kuvychko/session-beacon/host/tests/test_fixtures.py

"""Replay real Claude Code hook payloads through the state machine.

The payloads in tests/fixtures/hook_payloads.jsonl were captured from this
machine by running the daemon with --capture, not written by hand. That matters:
the published schema this project was originally built against disagrees with
what Claude Code 2.1.261 actually sends, and only a captured payload catches
that. See docs/claude-code-integration.md.

Conversation content is stripped at capture time, so the fixtures carry field
names and shapes and none of the text.
"""

from __future__ import annotations

import json
from pathlib import Path

import pytest

from beacon_host.capture import redact
from beacon_host.state import SessionStore, State

FIXTURES_DIR = Path(__file__).parent / "fixtures"
FIXTURES = FIXTURES_DIR / "hook_payloads.jsonl"
BACKGROUND_STOP = FIXTURES_DIR / "stop_with_background_tasks.json"
SUBAGENT_RUN = FIXTURES_DIR / "subagent_run.jsonl"


def load() -> dict[str, dict]:
    lines = FIXTURES.read_text(encoding="utf-8").splitlines()
    payloads = [json.loads(line) for line in lines if line.strip()]
    return {p["hook_event_name"]: p for p in payloads}


@pytest.fixture(scope="module")
def events() -> dict[str, dict]:
    return load()


def test_fixtures_cover_the_observed_lifecycle(events):
    assert set(events) == {
        "SessionStart", "UserPromptSubmit", "PermissionRequest", "PostToolUse",
        "PostToolBatch", "Notification", "Stop", "SessionEnd"
    }


def test_every_payload_has_the_fields_the_state_machine_reads(events):
    """session_id, cwd and hook_event_name are the three the store depends on."""
    for name, p in events.items():
        assert p.get("session_id"), name
        assert p.get("cwd"), name
        assert p.get("hook_event_name") == name


def test_real_lifecycle_drives_the_expected_states(events):
    """The sequence a session actually produces, replayed end to end."""
    store = SessionStore()
    sid = events["SessionStart"]["session_id"]

    store.apply_event(events["SessionStart"], 0)
    assert store.sessions[sid].state == State.STARTING
    assert store.sessions[sid].label == "session-beacon"

    store.apply_event(events["UserPromptSubmit"], 1)
    assert store.sessions[sid].state == State.WORKING
    # permission_mode rides along on most events and is captured for later use.
    assert store.sessions[sid].permission_mode == "default"

    store.apply_event(events["Stop"], 2)
    assert store.sessions[sid].state == State.IDLE

    store.apply_event(events["SessionEnd"], 3)
    assert store.sessions[sid].state == State.ENDED
    store.tick(3 + 31)
    assert sid not in store.sessions


def test_real_post_tool_use_marks_work_and_records_the_tool(events):
    """Everything in the payload that does not touch the filesystem."""
    store = SessionStore()
    p = events["PostToolUse"]
    store.apply_event(p, 0)
    s = store.sessions[p["session_id"]]
    assert s.state == State.WORKING
    assert s.last_tool == "Bash"
    assert s.permission_mode == "auto"
    # The captured cwd is a subdirectory of the repo, which is what makes the
    # label test below worth doing.
    assert s.cwd.replace("\\", "/").endswith("/host")


def test_real_payload_label_resolves_to_the_repository(events, tmp_path):
    """The captured cwd is a real absolute path from the machine that recorded
    it, and label resolution walks the filesystem looking for a `.git`. Replaying
    the payload as-is therefore passes only on that one machine: anywhere else
    the path does not exist, the walk finds nothing, and the label falls back to
    the directory basename `host`.

    So rebuild that shape under tmp_path and repoint the payload at it. The code
    path exercised is identical; the filesystem it walks is now the test's own.
    """
    repo = tmp_path / "session-beacon"
    (repo / ".git").mkdir(parents=True)
    sub = repo / "host"
    sub.mkdir()

    payload = {**events["PostToolUse"], "cwd": str(sub)}
    store = SessionStore()
    store.apply_event(payload, 0)

    assert store.sessions[payload["session_id"]].label == "session-beacon"


def test_fixtures_carry_no_conversation_content(events):
    """A guard against a future capture change leaking transcripts into the repo.
    Redacted values are markers like '<str len=22>', never the text itself."""
    for f in sorted(FIXTURES_DIR.iterdir()):
        blob = f.read_text(encoding="utf-8")
        for leak in ("igork", "AppData", "C:\\\\Users"):
            assert leak not in blob, f"{f.name} leaks {leak!r}"

    for name, p in events.items():
        for field in ("prompt", "user_prompt", "last_assistant_message", "tool_response"):
            if field in p:
                assert str(p[field]).startswith("<"), f"{name}.{field} is not redacted"
        for k, v in (p.get("tool_input") or {}).items():
            assert str(v).startswith("<"), f"{name}.tool_input.{k} is not redacted"
        # A batch nests both of the above one level down, once per call.
        for i, call in enumerate(p.get("tool_calls") or []):
            if "tool_response" in call:
                msg = f"{name}.tool_calls[{i}].tool_response is not redacted"
                assert str(call["tool_response"]).startswith("<"), msg
            for k, v in (call.get("tool_input") or {}).items():
                msg = f"{name}.tool_calls[{i}].tool_input.{k} is not redacted"
                assert str(v).startswith("<"), msg


def test_the_real_post_tool_batch_is_a_rejected_call(events):
    """Captured by running the daemon with --capture on a spare port and driving
    a headless `claude -p` whose Bash call was refused, which is the same
    resolution a rejected prompt produces: the tool never ran, so the payload
    carries the refusal as its `tool_response` and no PostToolUse accompanies it.
    """
    p = events["PostToolBatch"]
    call = p["tool_calls"][0]
    assert call["tool_name"] == "Bash"
    assert call["tool_response"].startswith("<")
    assert call["tool_input"]["command"].startswith("<")


def test_a_rejected_prompt_clears_the_red_row(events):
    """The bug, replayed from real payloads.

    A plan rejected with feedback answers the prompt without running anything.
    Before PostToolBatch was registered nothing arrived at that moment, so the
    row stayed red for as long as Claude then spent thinking -- 68 seconds, in
    the session that turned this up.
    """
    store = SessionStore()
    store.apply_event(events["UserPromptSubmit"], 0)
    sid = events["UserPromptSubmit"]["session_id"]

    store.apply_event({**events["PermissionRequest"], "session_id": sid}, 1)
    store.tick(200)
    assert store.sessions[sid].state == State.NEEDS_HELD

    store.apply_event({**events["PostToolBatch"], "session_id": sid}, 300)
    assert store.sessions[sid].state == State.WORKING
    assert store.sessions[sid].last_tool == "Bash"


def test_redact_strips_a_batch_of_command_lines_and_output():
    """The raw shape, before redaction: `tool_calls` carries a command line and
    the text it printed, one level below the top-level names that were already
    covered. Built by hand *because* it is the unredacted form -- the committed
    fixture is the captured payload this produces."""
    raw = {"hook_event_name": "PostToolBatch", "session_id": "s", "cwd": "C:/x",
           "tool_calls": [{"tool_name": "Bash", "tool_use_id": "toolu_1",
                           "tool_input": {"command": "git log --oneline",
                                          "description": "list commits"},
                           "tool_response": "4a26044 Capture the permission prompt"}]}
    call = redact(raw)["tool_calls"][0]
    assert call["tool_name"] == "Bash"
    assert call["tool_use_id"] == "toolu_1"
    assert call["tool_input"] == {"command": "<str len=17>",
                                  "description": "<str len=12>"}
    assert call["tool_response"] == "<str len=37>"


def test_redact_strips_a_shell_tasks_command_line():
    """`background_tasks` is not only subagents. A task of type `shell` carries
    the command line it is running, up to a thousand characters of it, one level
    below the top-level names CONTENT_FIELDS already covers -- the same leak
    `ruleContent` was. The committed fixtures have no shell task, so nothing
    caught this until the type vocabulary was checked against the CLI's schema.
    """
    raw = {"hook_event_name": "Stop", "session_id": "s", "cwd": "C:/x",
           "background_tasks": [
               {"id": "b1a2", "type": "shell", "status": "running",
                "command": "npm run dev -- --port 3000",
                "description": "dev server"},
               {"id": "s1a2", "type": "monitor", "status": "running",
                "server": "artifacts", "tool": "watch",
                "description": "Cursor Rollout Stocktake"}]}
    tasks = redact(raw)["background_tasks"]
    # The shape the state machine reads survives; the free text does not.
    assert [t["type"] for t in tasks] == ["shell", "monitor"]
    assert [t["status"] for t in tasks] == ["running", "running"]
    assert tasks[0]["command"] == "<str len=26>"
    assert tasks[0]["description"] == "<str len=10>"
    assert tasks[1]["server"] == "artifacts" and tasks[1]["tool"] == "watch"
    assert tasks[1]["description"] == "<str len=24>"


def test_redact_strips_a_session_crons_prompt():
    """`session_crons` rides on the same events as `background_tasks` and holds
    the text of a /loop, a CronCreate or a ScheduleWakeup. `prompt` was already
    named in CONTENT_FIELDS, but that only covers the top level, so the list
    went through untouched. Every committed fixture has it empty."""
    raw = {"hook_event_name": "Stop", "session_id": "s", "cwd": "C:/x",
           "session_crons": [{"id": "c1", "schedule": "*/5 * * * *",
                              "recurring": True,
                              "prompt": "check the deploy and report back"}]}
    cron = redact(raw)["session_crons"][0]
    assert cron["schedule"] == "*/5 * * * *" and cron["recurring"] is True
    assert cron["prompt"] == "<str len=32>"


def test_redact_is_idempotent(events):
    """Re-redacting a fixture must not corrupt it, so fixtures can be refreshed
    from a capture file without special-casing."""
    for p in events.values():
        assert redact(p) == p


@pytest.fixture(scope="module")
def background_stop() -> dict:
    return json.loads(BACKGROUND_STOP.read_text(encoding="utf-8"))


def test_background_stop_fixture_is_a_real_capture(background_stop):
    """Captured from this machine by ending a turn with a subagent running.

    The empty list in hook_payloads.jsonl showed the field existed but not what
    a populated one looks like, which is why the fix waited on this rather than
    guessing the shape.
    """
    tasks = background_stop["background_tasks"]
    assert background_stop["hook_event_name"] == "Stop"
    assert tasks and tasks[0]["status"] == "running"
    assert tasks[0]["type"] == "subagent"
    # Free text is stripped; the fields the state machine reads survive.
    assert tasks[0]["description"].startswith("<")


def test_a_turn_ending_on_a_running_agent_does_not_go_idle(background_stop, events):
    """The false red, replayed from real payloads end to end."""
    store = SessionStore()
    store.apply_event(events["UserPromptSubmit"], 0)
    sid = events["UserPromptSubmit"]["session_id"]

    store.apply_event({**background_stop, "session_id": sid}, 1)
    assert store.sessions[sid].state == State.WORKING

    store.apply_event({"hook_event_name": "Notification", "session_id": sid,
                       "cwd": background_stop["cwd"],
                       "notification_type": "idle_prompt"}, 2)
    assert store.sessions[sid].state == State.WORKING

    # The real Stop from the earlier capture, with the list empty, ends the turn.
    store.apply_event({**events["Stop"], "session_id": sid}, 3)
    assert store.sessions[sid].state == State.IDLE


def test_background_stop_fixture_is_already_redacted(background_stop):
    assert redact(background_stop) == background_stop


def test_the_real_idle_prompt_drives_the_attention_state(events):
    """The attention path, from a captured payload rather than a hand-written one.

    `idle_prompt` was on the "present in the binary but never seen firing" list
    for a long time, which made the red row the one part of the display resting
    on reasoning. This is that payload.
    """
    n = events["Notification"]
    assert n["notification_type"] == "idle_prompt"

    store = SessionStore()
    store.apply_event(events["UserPromptSubmit"], 0)
    sid = events["UserPromptSubmit"]["session_id"]
    store.apply_event({**n, "session_id": sid}, 1)
    assert store.sessions[sid].state == State.NEEDS_INPUT


def test_a_repeated_real_idle_prompt_does_not_restart_the_pulse(events):
    """Captured twice for one session, minutes apart, which is why the ladder
    only arms on entry: re-arming on each would pulse for as long as the session
    sits unanswered."""
    n = events["Notification"]
    store = SessionStore()
    sid = "repeat-test"
    store.apply_event({**n, "session_id": sid}, 0)
    store.tick(200)
    assert store.sessions[sid].state == State.NEEDS_HELD

    store.apply_event({**n, "session_id": sid}, 210)
    store.tick(220)
    assert store.sessions[sid].state == State.NEEDS_HELD
    assert store.snapshot(220)["s"][0]["age"] == 220


def test_the_real_permission_request_drives_the_attention_state(events):
    """The dedicated attention event, from a captured payload.

    Triggered by switching the session to manual approval and running a command
    that needs one, with the daemon capturing.
    """
    p = events["PermissionRequest"]
    assert p["tool_name"] == "Bash"
    assert p["permission_mode"] == "default"

    store = SessionStore()
    store.apply_event(events["UserPromptSubmit"], 0)
    sid = events["UserPromptSubmit"]["session_id"]
    store.apply_event({**p, "session_id": sid}, 1)
    assert store.sessions[sid].state == State.NEEDS_INPUT

    # Answering it, by letting the tool run, clears the row.
    store.apply_event({**events["PostToolUse"], "session_id": sid}, 2)
    assert store.sessions[sid].state == State.WORKING


def test_permission_suggestions_carry_no_command_text(events):
    """`permission_suggestions` holds the rule Claude Code offers to add, and
    the rule is built from the command line -- the very thing redacting
    `tool_input` exists to strip. The shape survives; the text does not."""
    sug = events["PermissionRequest"]["permission_suggestions"][0]
    assert sug["behavior"] == "allow"
    assert sug["rules"][0]["toolName"] == "Bash"
    assert sug["rules"][0]["ruleContent"].startswith("<")


# ---- a real session that spawned a subagent -------------------------------


@pytest.fixture(scope="module")
def subagent_run() -> list[dict]:
    """One captured session, start to end, that used an Explore subagent.

    Kept as a sequence rather than folded into hook_payloads.jsonl, which is
    keyed one payload per event name: the order is the evidence here, and the
    run contains two PostToolUse events that must stay distinguishable.
    """
    lines = SUBAGENT_RUN.read_text(encoding="utf-8").splitlines()
    return [json.loads(line) for line in lines if line.strip()]


def test_subagent_events_carry_the_parents_session_id(subagent_run):
    """The root cause, in captured form. Everything a subagent does arrives
    under the session_id of the session that spawned it, so `agent_id` is the
    only thing that separates the two."""
    assert len({p["session_id"] for p in subagent_run}) == 1

    tagged = [p for p in subagent_run if p.get("agent_id")]
    assert {p["hook_event_name"] for p in tagged} == {
        "SubagentStart", "PostToolUse", "PostToolBatch", "SubagentStop"}
    assert len({p["agent_id"] for p in tagged}) == 1
    assert all(p["agent_type"] == "Explore" for p in tagged)

    # The parent's own events carry neither field, including the PostToolUse
    # for the Agent call itself, which lands after the subagent has stopped.
    parent = [p for p in subagent_run if not p.get("agent_id")]
    assert all("agent_type" not in p for p in parent)
    assert [p["tool_name"] for p in parent if p["hook_event_name"] == "PostToolUse"] \
        == ["Agent"]


def test_the_real_subagent_stop_carries_background_tasks(subagent_run):
    """It is the same list Stop carries, which is what makes it a resync point.

    Present and empty here: this agent ran in the foreground, so it was never
    registered as background work. A populated one is still unobserved, which is
    why SubagentStop excludes the agent it is reporting rather than trusting the
    list to have dropped it already.
    """
    stop = next(p for p in subagent_run if p["hook_event_name"] == "SubagentStop")
    assert stop["background_tasks"] == []
    assert stop["agent_id"] and stop["agent_transcript_path"].startswith("<path>")


def test_the_real_subagent_run_never_disturbs_a_waiting_row(subagent_run):
    """The reported bug, replayed against real payloads.

    The parent raises a permission prompt, and the subagent it launched earlier
    goes on emitting tool calls under the parent's session_id. Every one of them
    used to repaint the row WORKING, so a session genuinely blocked on a human
    showed blue on the display -- the exact case the device exists for.
    """
    store = SessionStore()
    sid = subagent_run[0]["session_id"]
    cwd = subagent_run[0]["cwd"]
    clock = iter(range(1, 100))

    for payload in subagent_run:
        if payload["hook_event_name"] == "SubagentStart":
            # The parent blocks on a prompt of its own while the agent works.
            store.apply_event({"hook_event_name": "PermissionRequest",
                               "session_id": sid, "cwd": cwd,
                               "tool_name": "Bash"}, next(clock))
            assert store.sessions[sid].state == State.NEEDS_INPUT

        store.apply_event(payload, next(clock))

        if payload.get("agent_id"):
            assert store.sessions[sid].state == State.NEEDS_INPUT, \
                f"{payload['hook_event_name']} from a subagent cleared the row"
        elif payload["hook_event_name"] == "PostToolUse":
            # The parent's own PostToolUse, for the Agent call itself, is
            # what finally answers the prompt -- and it arrives only once
            # the subagent has stopped.
            assert store.sessions[sid].state == State.WORKING

    assert store.sessions[sid].state == State.ENDED


def test_the_real_subagent_run_is_already_redacted(subagent_run):
    for payload in subagent_run:
        assert redact(payload) == payload
